Cocotrilito/The-Dichotomy-Split/images/ALIEXPRESS CART.png

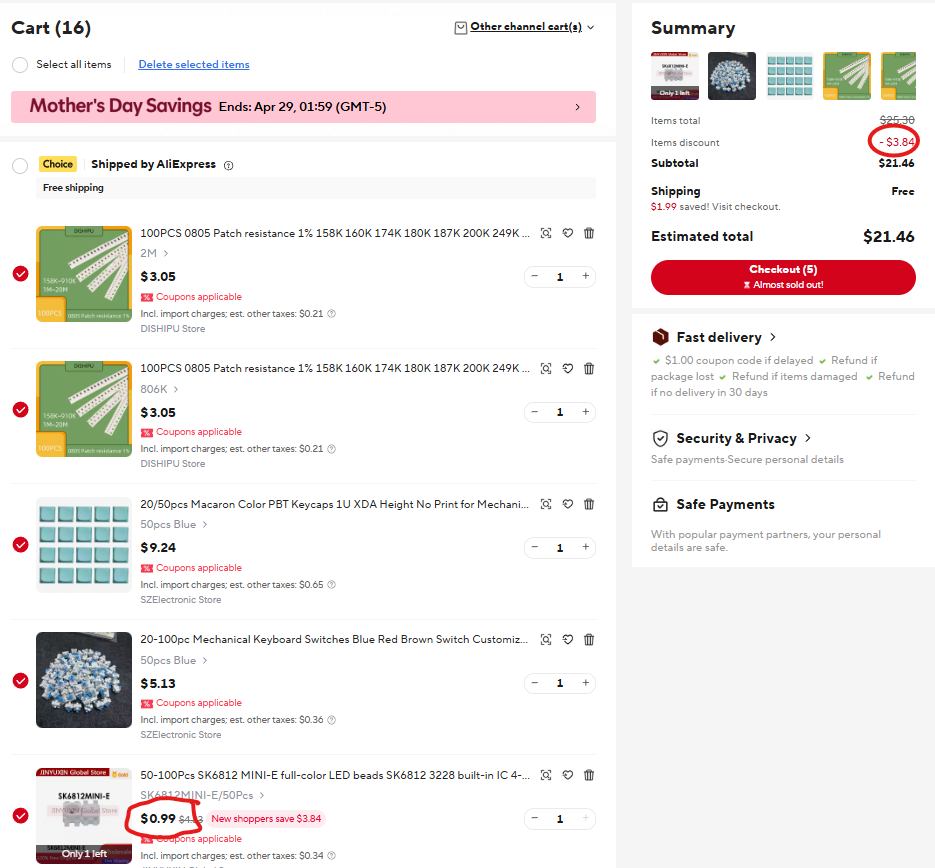
images/ALIEXPRESS CART.png
