Cocotrilito/The-Dichotomy-Split/images/AMAZON CART.png

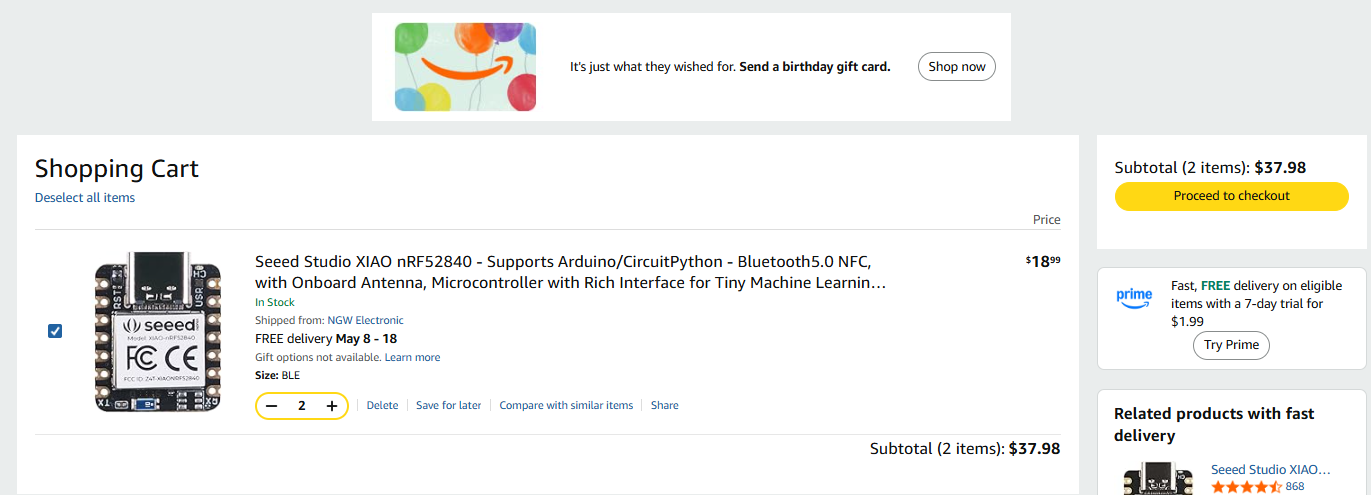
images/AMAZON CART.png
