Cocotrilito/The-Dichotomy-Split/images/art2.png

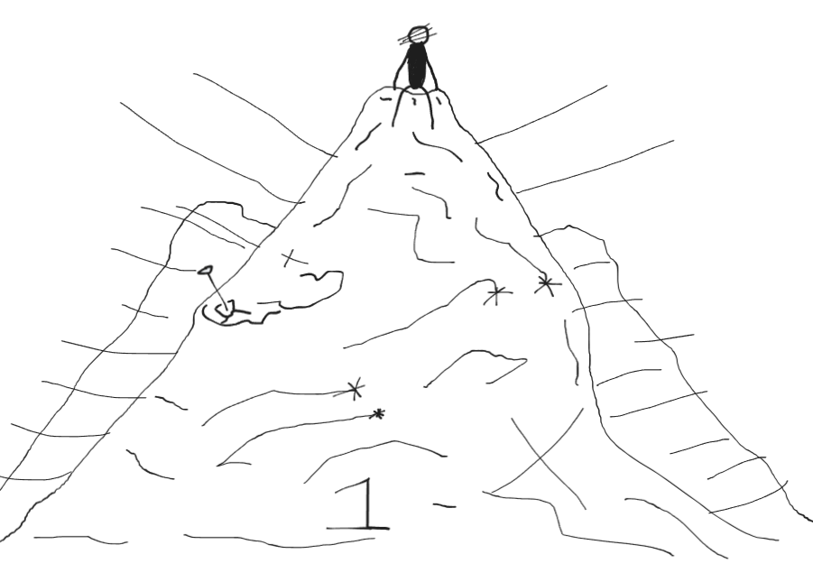
images/art2.png
