Cocotrilito/The-Dichotomy-Split/images/JLCPCB CART.png

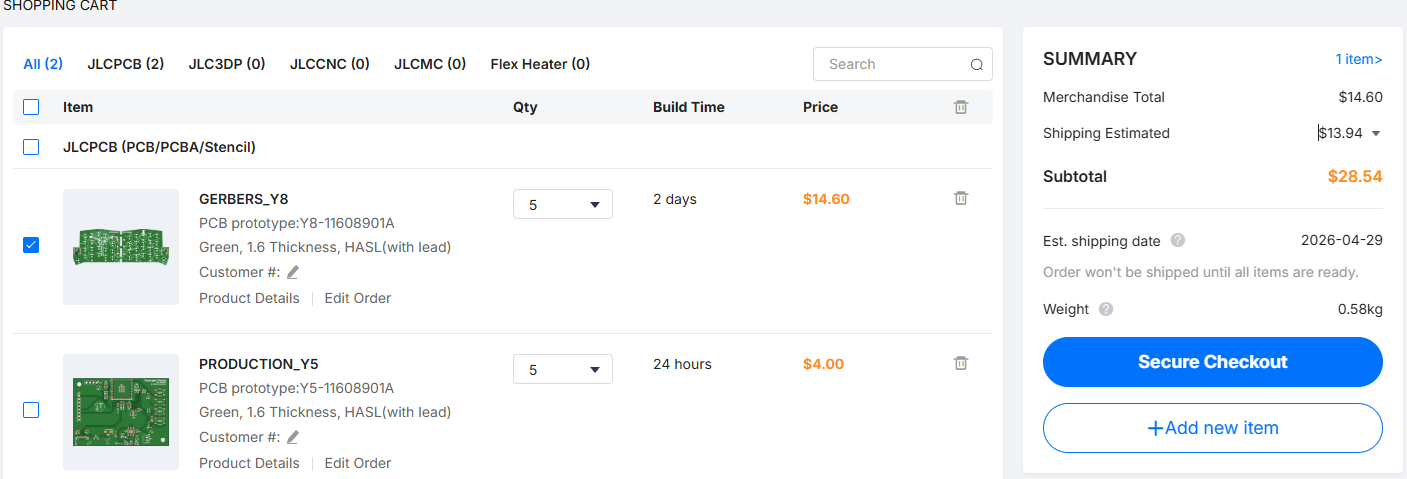
images/JLCPCB CART.png
